Emmemad/ATS-20_Schematic/ATS-20+/ATS-20_Plus_Trace/Images/encoder_ribbon_cable_socket.jpg

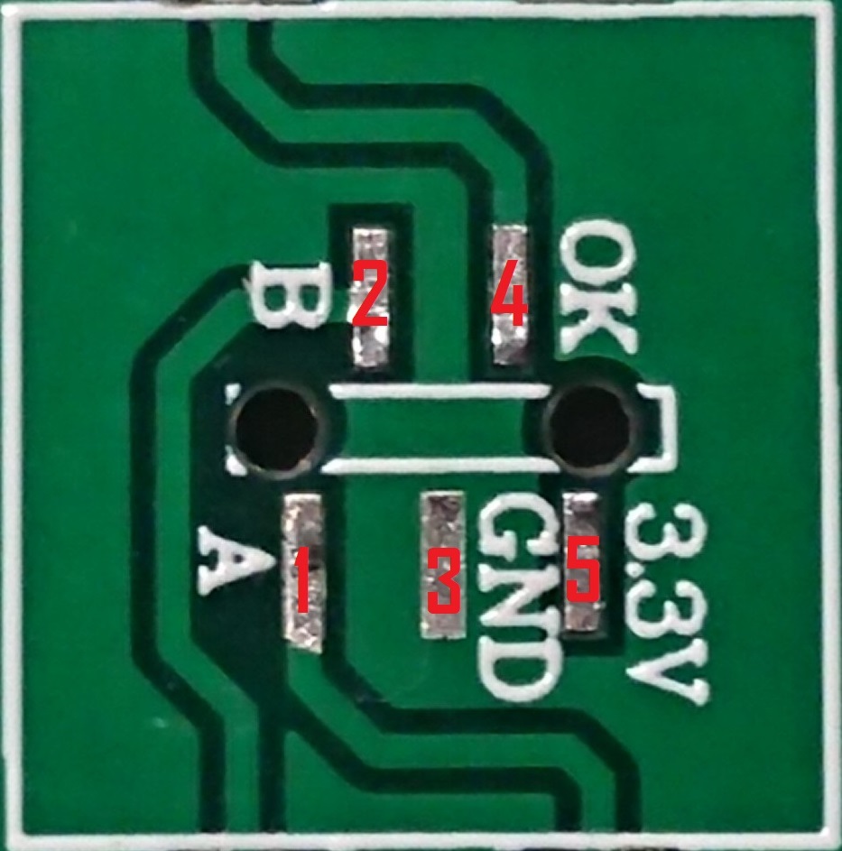
ATS-20+/ATS-20_Plus_Trace/Images/encoder_ribbon_cable_socket.jpg
