Emmemad/ATS-20_Schematic/ATS-20+/ATS-20_Plus_Trace/Images/ribbon_cable_socket.png

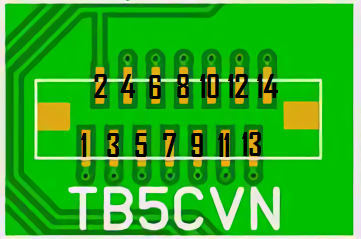
ATS-20+/ATS-20_Plus_Trace/Images/ribbon_cable_socket.png
