Emmemad/ATS-20_Schematic/ATS-20+/Pictures/ATS-20+_charging_port.png

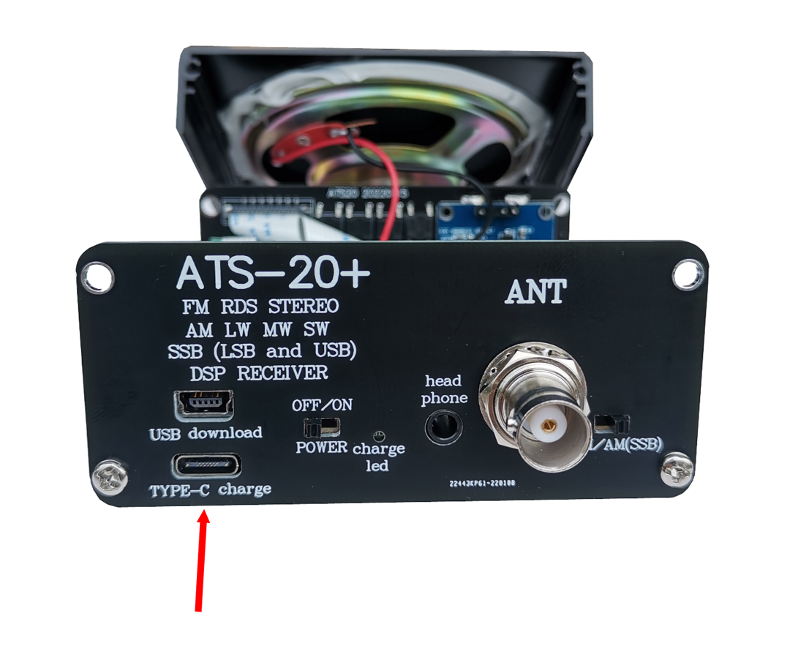
ATS-20+/Pictures/ATS-20+_charging_port.png
