Emmemad/ATS-20_Schematic/ATS-20+/Pictures/ATS-20+_encoder.jpg

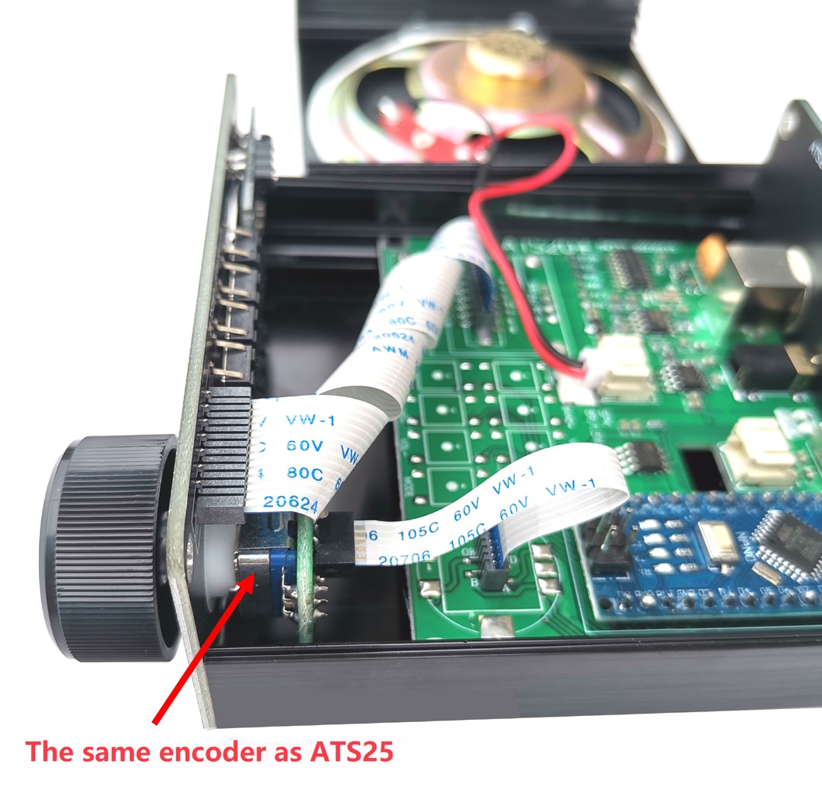
ATS-20+/Pictures/ATS-20+_encoder.jpg
