Emmemad/ATS-20_Schematic/ATS-20+/Pictures/ATS-20+_filter_amplifier.jpg

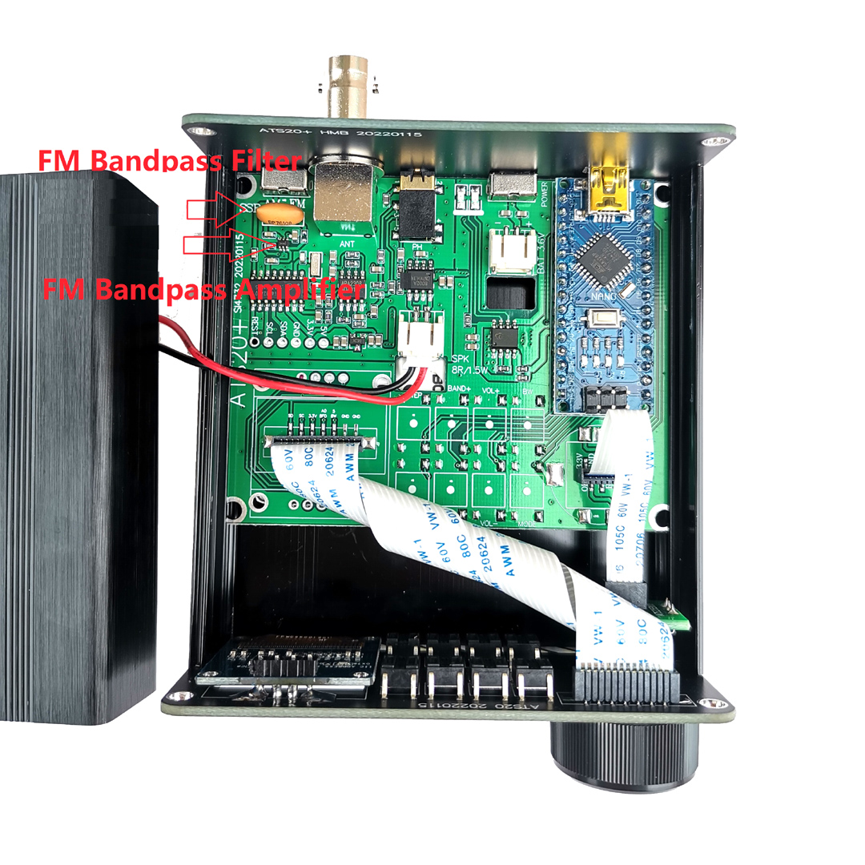
ATS-20+/Pictures/ATS-20+_filter_amplifier.jpg
