Emmemad/ATS-20_Schematic/ATS-20+/Pictures/Board_photos/ATS-20_Plus_7.JPG

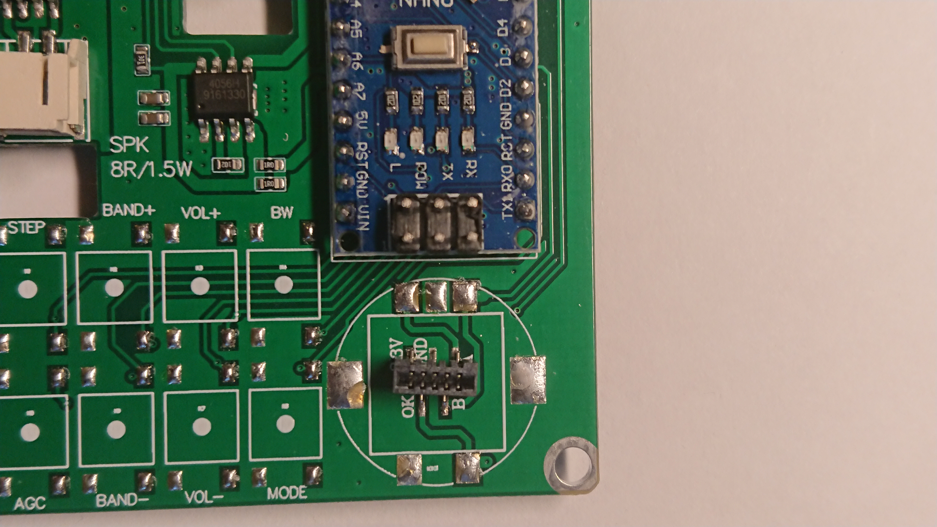
ATS-20+/Pictures/Board_photos/ATS-20_Plus_7.JPG
