Emmemad/ATS-20_Schematic/ATS-20/Pictures/ATS-20_back_antenna.jpg

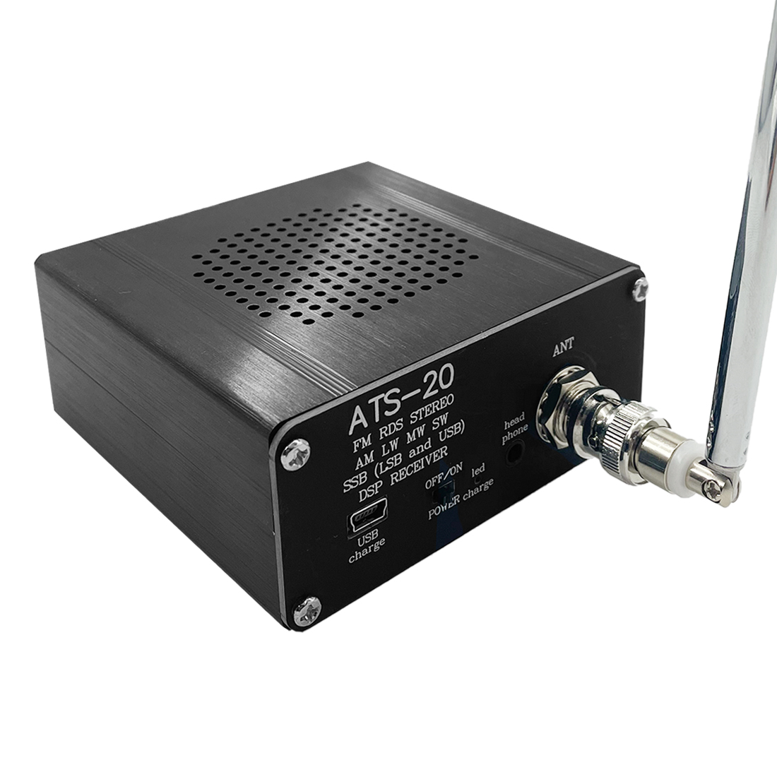
ATS-20/Pictures/ATS-20_back_antenna.jpg
