Emmemad/ATS-20_Schematic/ATS-20/Pictures/ATS-20_cover_removed.JPG

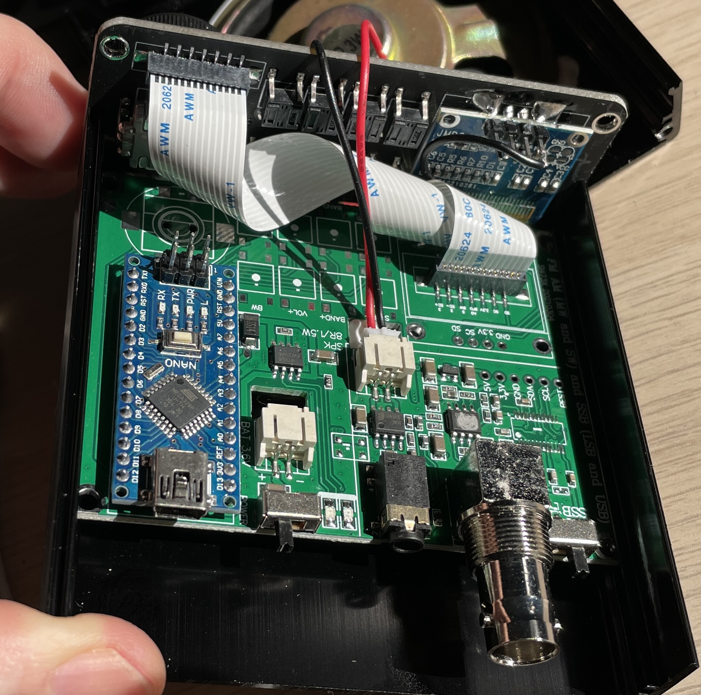
ATS-20/Pictures/ATS-20_cover_removed.JPG
