Emmemad/ATS-20_Schematic/ATS-20/Pictures/PCB/Original/1110541948202.jpg

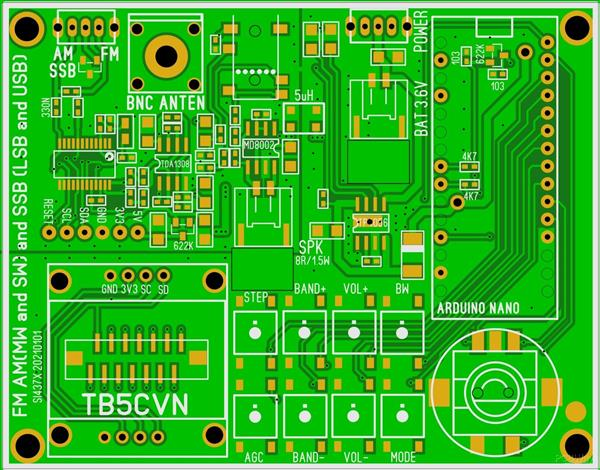
ATS-20/Pictures/PCB/Original/1110541948202.jpg
