Emmemad/ATS-20_Schematic/ATS-20/Pictures/PCB/Original/1111073910710.jpg

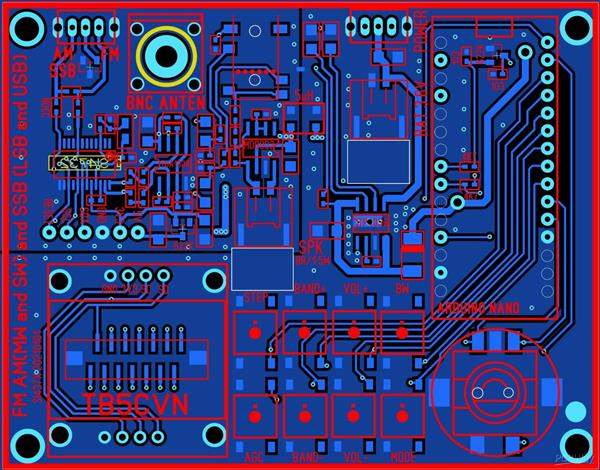
ATS-20/Pictures/PCB/Original/1111073910710.jpg
