Emmemad/ATS-20_Schematic/ATS-20/Pictures/PCB/Original/1111167664805.jpg

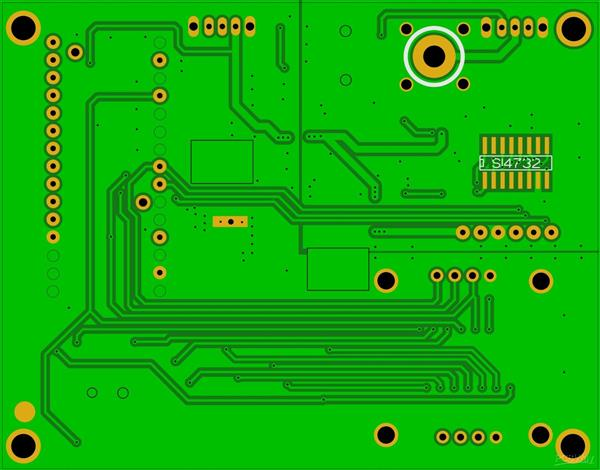
ATS-20/Pictures/PCB/Original/1111167664805.jpg
