Emmemad/ATS-20_Schematic/ATS-20/Pictures/PCB/Traceback enhanced/TB5CVN_back_enhanced_mirrored.png

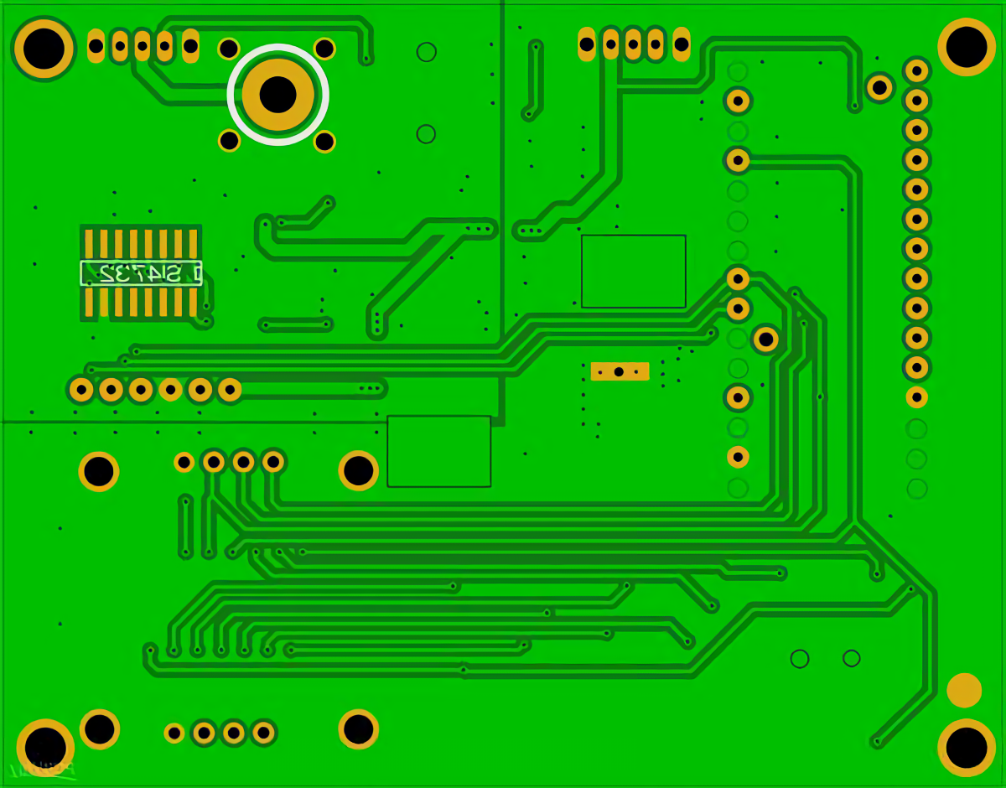
ATS-20/Pictures/PCB/Traceback enhanced/TB5CVN_back_enhanced_mirrored.png
