Emmemad/ATS-20_Schematic/ATS-20/Pictures/Robert Richmond's photos/Si4732-Internal-Photos-Robert-Richmond-2.jpeg

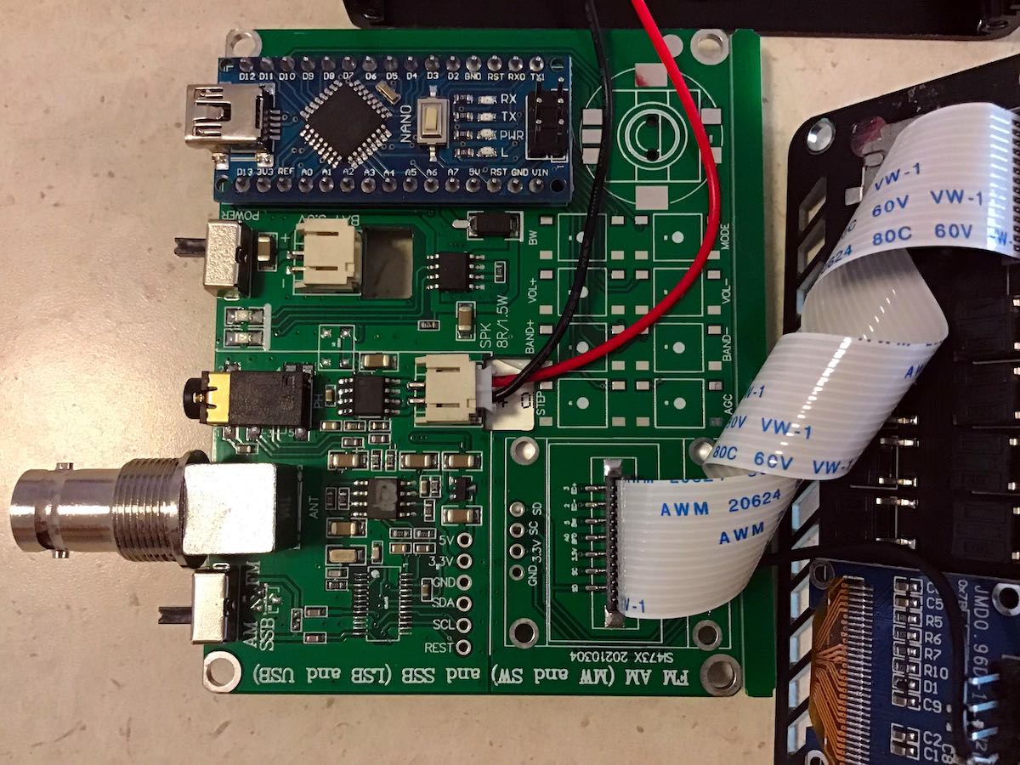
ATS-20/Pictures/Robert Richmond's photos/Si4732-Internal-Photos-Robert-Richmond-2.jpeg
