Emmemad/ATS-20_Schematic/ATS-20+/ATS-20_Plus_Trace/ATS-20_Plus_Trace.kicad_sch

## KiCad design ATS-20+/ATS-20_Plus_Trace/ATS-20_Plus_Trace.kicad_sch (2022-08-20)

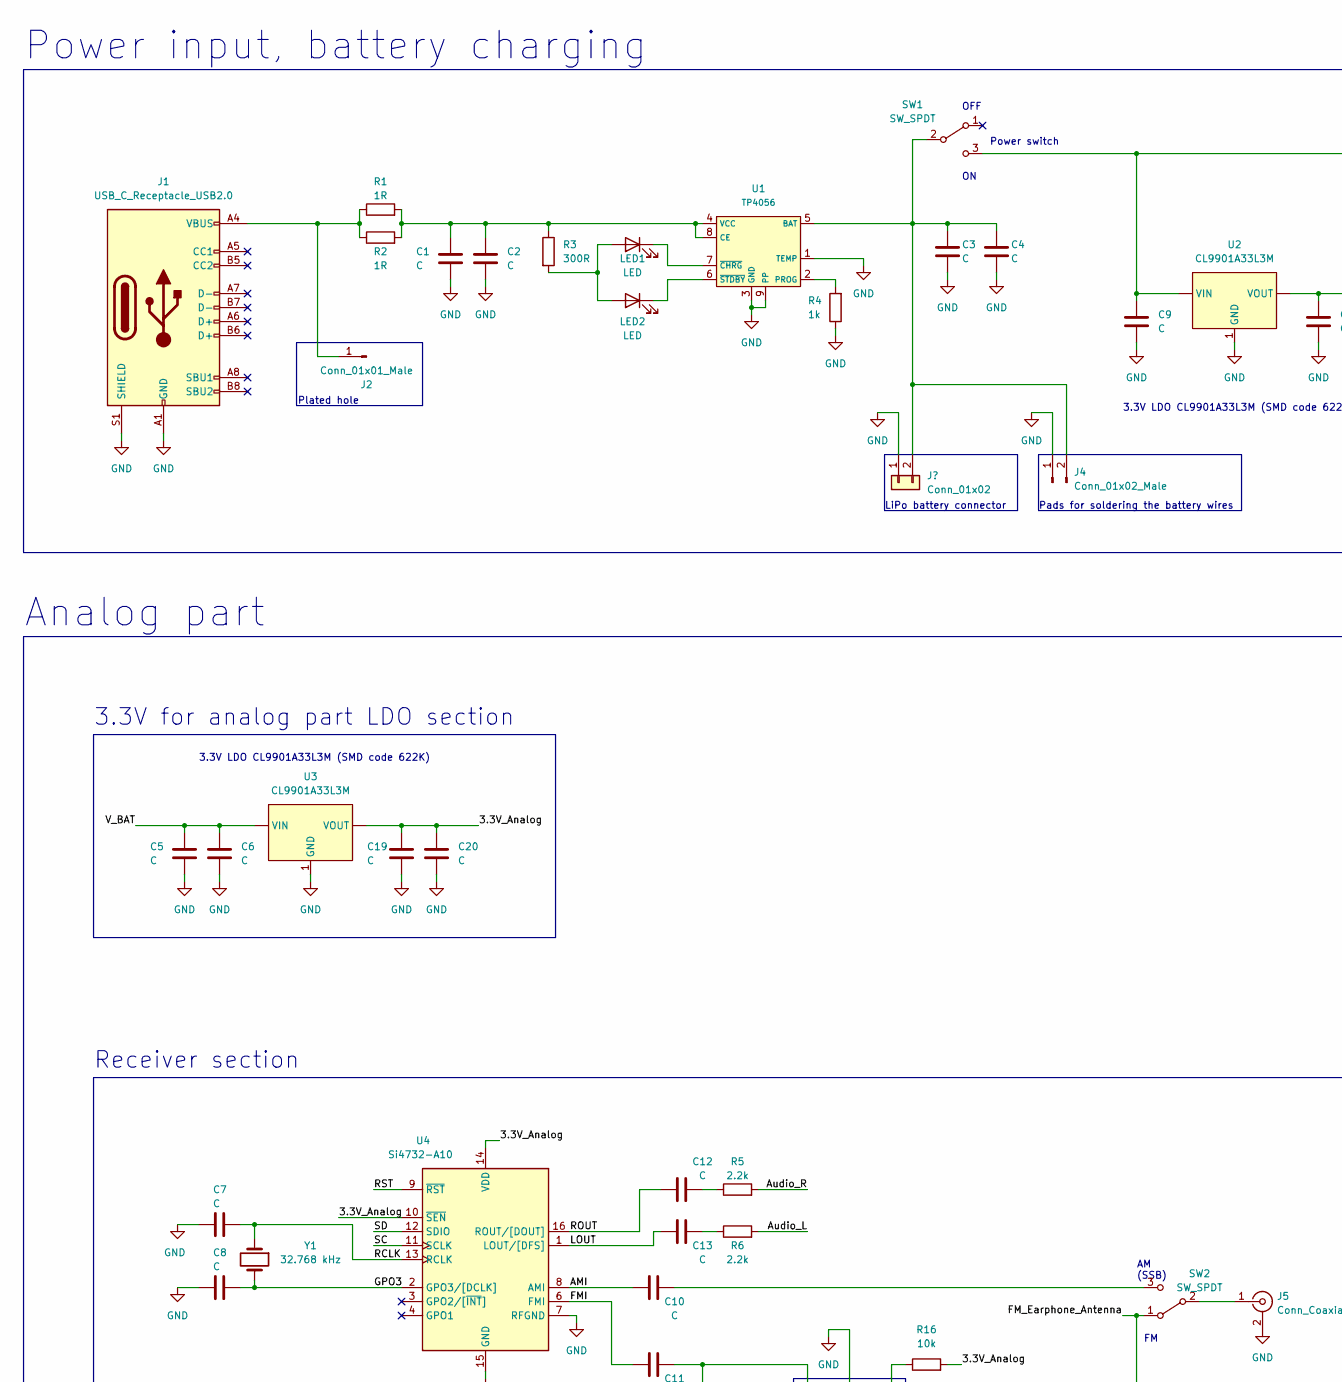
[picture p44: schematic ATS-20_Plus_Trace.kicad_sch, part in row 1, column 1]

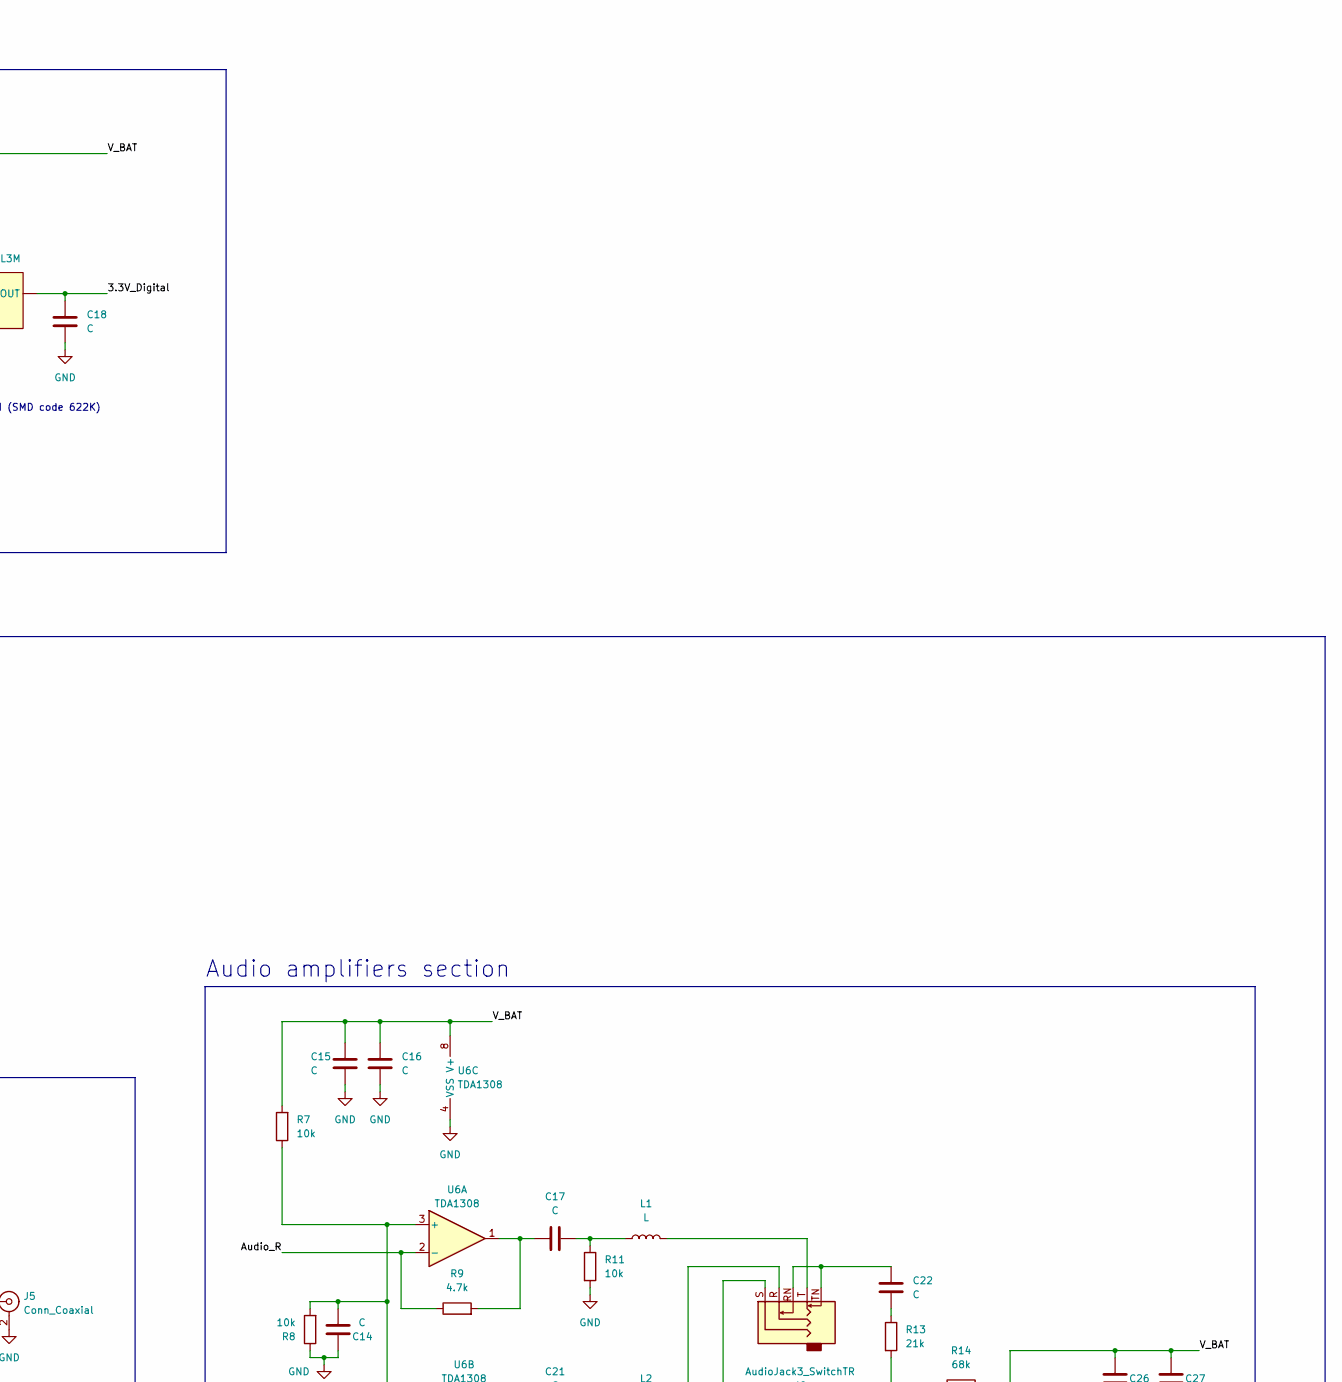
[picture p45: schematic ATS-20_Plus_Trace.kicad_sch, part in row 1, column 2]

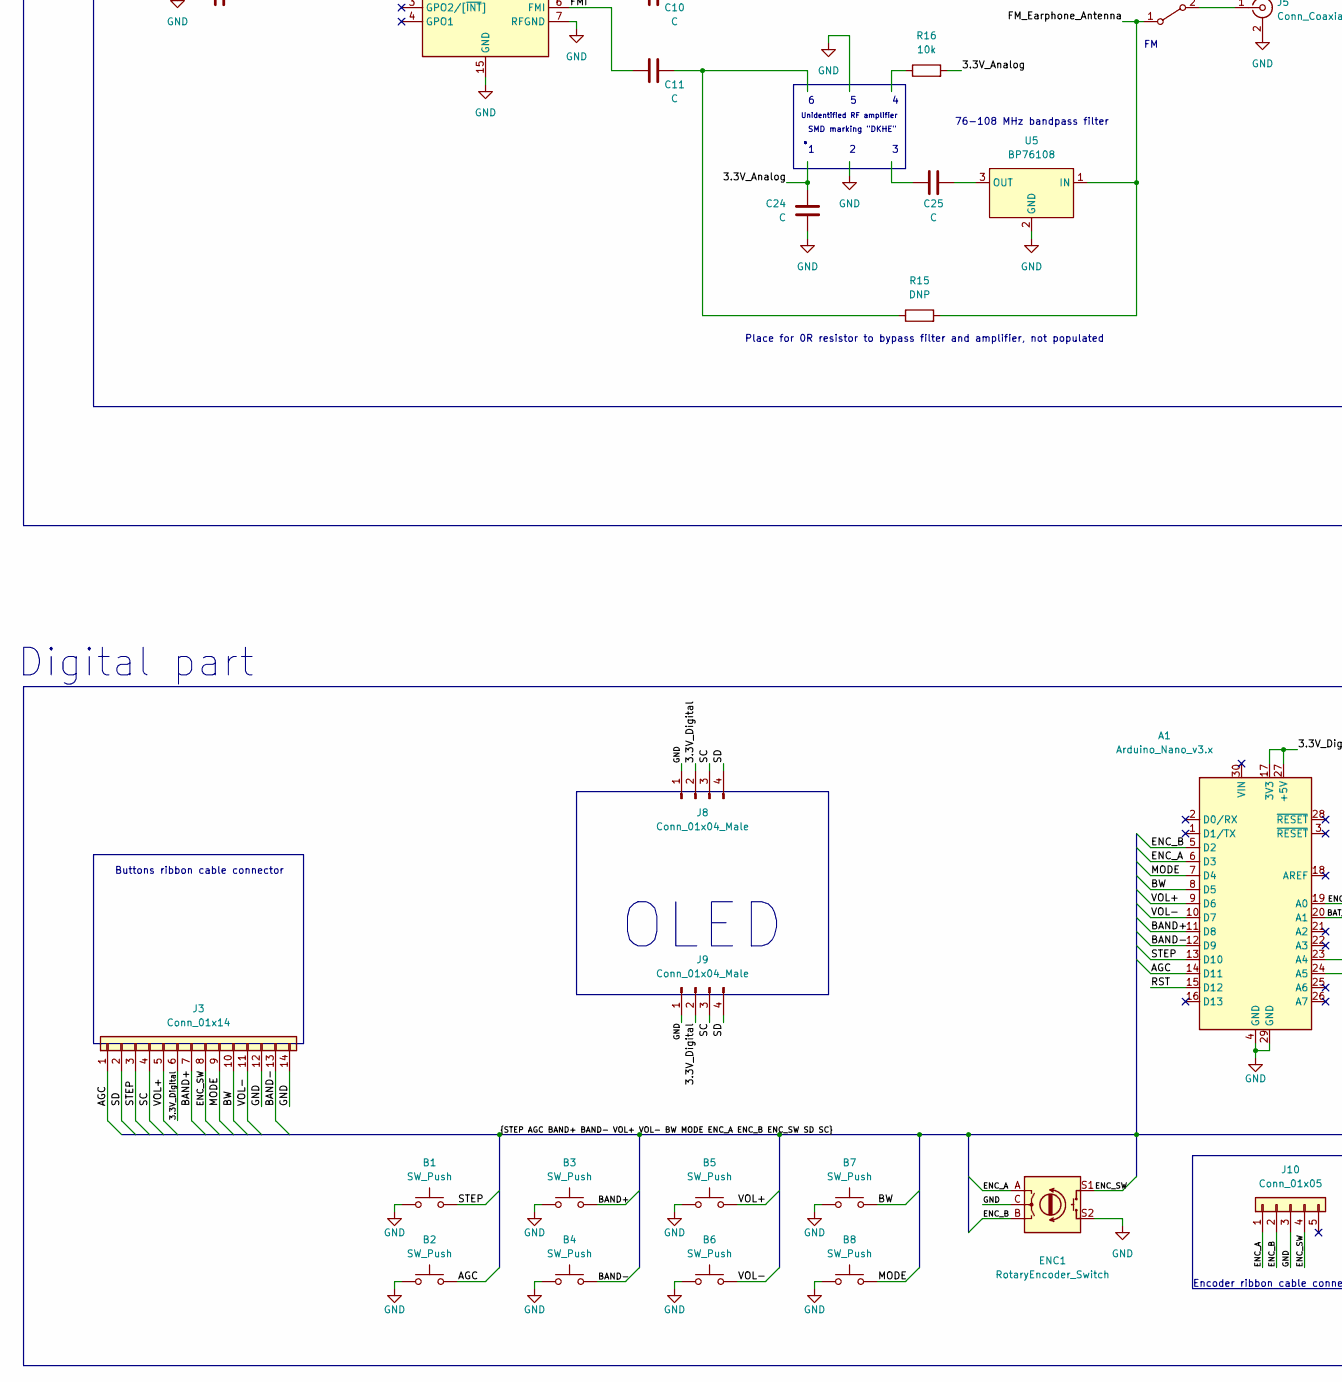
[picture p46: schematic ATS-20_Plus_Trace.kicad_sch, part in row 2, column 1]

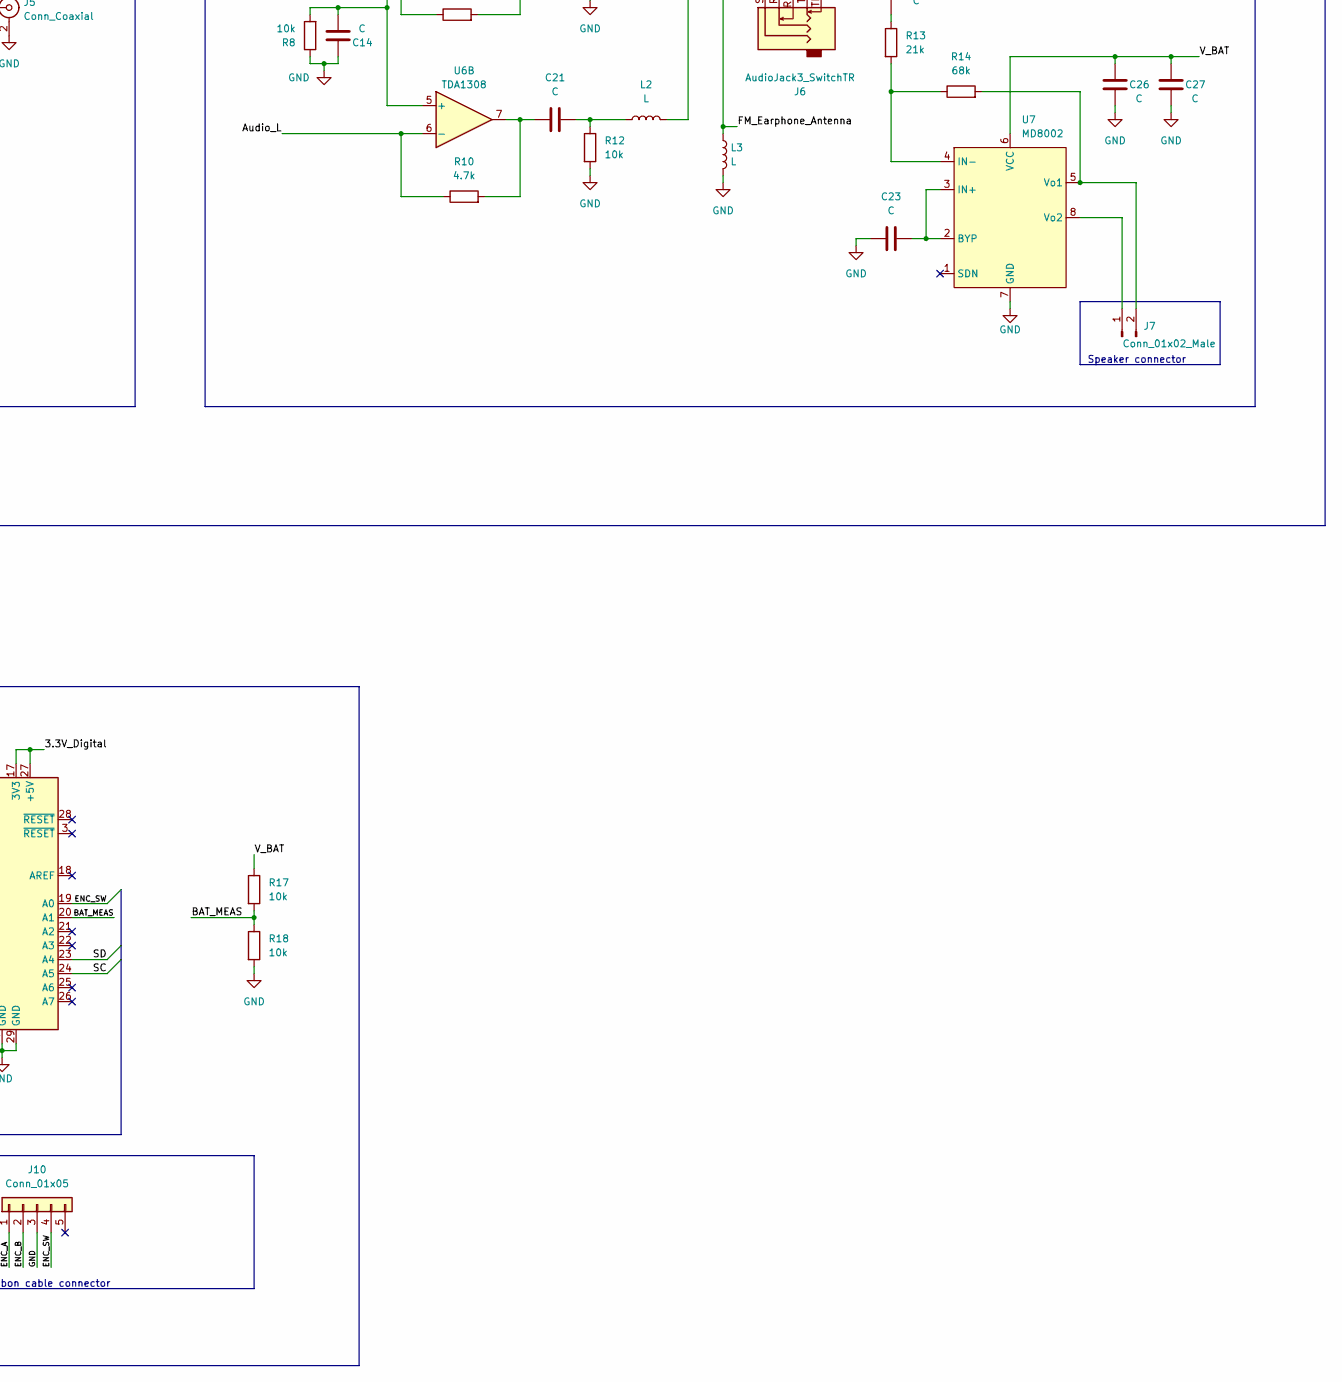
[picture p47: schematic ATS-20_Plus_Trace.kicad_sch, part in row 2, column 2]

Parts:
A1: Arduino_Nano_v3.x; Arduino_Nano
B1, B2, B3, B4, B5, B6, B7, B8: SW_Push
C1, C2, C3, C4, C5, C6, C7, C8, C9, C10, C11, C12, C13, C14, C15, C16, C17, C18, C19, C20, C21, C22, C23, C24, C25, C26, C27: C
ENC1: RotaryEncoder_Switch
J1: USB_C_Receptacle_USB2.0
J2: Conn_01x01_Male
J3: Conn_01x14; Molex_PicoBlade_53398-1471_1x14-1MP_P1.25mm_Vertical
J4, J7: Conn_01x02_Male
J5: Conn_Coaxial
J6: AudioJack3_SwitchTR; Jack_3.5mm_PJ311_Horizontal
J8, J9: Conn_01x04_Male
J10: Conn_01x05
L1, L2, L3: L
LED1, LED2: LED
R1, R2: 1R
R3: 300R
R4: 1k
R5, R6: 2.2k
R7, R8, R11, R12, R16, R17, R18: 10k
R9, R10: 4.7k
R13: 21k
R14: 68k
R15: DNP
SW1, SW2: SW_SPDT
U1: TP4056; SOIC-8-1EP_3.9x4.9mm_P1.27mm_EP2.29x3mm
U2, U3: CL9901A33L3M
U4: Si4732-A10; SOIC-16_4.55x10.3mm_P1.27mm
U5: BP76108
U6: TDA1308
U7: MD8002
Y1: 32.768 kHz

Connections:
3.3V_Analog: C19.1, C20.1, C24.1, R16.2, U3. (VIN), U4.10 (~SEN), U4.14 (VDD)
3.3V_Digital: A1.17 (3V3), A1.27 (+5V), C18.1, J3.6, J8.2, J9.2, U2. (VIN)
AGC: A1.14 (D11), B2.2, J3.1
AMI: C10.1, U4.8 (AMI)
Audio_L: R6.2, R10.1, U6.6 (-)
Audio_R: R5.2, R9.1, U6.2 (-)
BAND+: A1.11 (D8), B3.2, J3.7
BAND-: A1.12 (D9), B4.2, J3.13
BAT_MEAS: A1.20 (A1), R17.2, R18.1
BW: A1.8 (D5), B7.2, J3.10
ENC_A: A1.6 (D3), ENC1.A, J10.1
ENC_B: A1.5 (D2), ENC1.B, J10.2
ENC_SW: A1.19 (A0), ENC1.S1, J3.8, J10.4
FMI: C11.1, U4.6 (FMI)
FM_Earphone_Antenna: J6.S, L3.1, R15.2, SW2.1 (A), U5.1 (IN)
GND: A1.4 (GND), A1.29 (GND), B1.1, B2.1, B3.1, B4.1, B5.1, B6.1, B7.1, B8.1, C1.1, C2.1, C3.1, C4.1, C5.2, C6.2, C7.2, C8.2, C9.2, C14.1, C15.2, C16.2, C18.2, C19.2, C20.2, C23.2, C24.2, C26.2, C27.2, ENC1.C, ENC1.S2, J1.A1 (GND), J1.A12 (GND), J1.B1 (GND), J1.B12 (GND), J1.S1 (SHIELD), J3.12, J3.14, J4.1, J5.2 (Ext), J8.1, J9.1, J10.3, L3.2, R4.1, R8.1, R11.2, R12.2, R18.2, U1.1 (TEMP), U1.3 (GND), U1.9 (PP), U2.1 (GND), U3.1 (GND), U4.7 (RFGND), U4.15 (GND), U5.2 (GND), U6.4 (VSS), U7.7 (GND)
GPO3: C8.1, U4.2 (GPO3/[DCLK]), Y1.2
LOUT: C13.1, U4.1 (LOUT/[DFS])
MODE: A1.7 (D4), B8.2, J3.9
unnamed: C1.2, C2.2, R1.2, R2.2, R3.1, U1.4 (VCC), U1.8 (CE)
unnamed: C3.2, C4.2, J4.2, SW1.2 (B), U1.5 (BAT)
unnamed: C10.2, SW2.3 (C)
unnamed: C11.2, R15.1
unnamed: C12.2, R5.1
unnamed: C13.2, R6.1
unnamed: C14.2, R7.1, R8.2, U6.3 (+), U6.5 (+)
unnamed: C17.1, R9.2, U6.1
unnamed: C17.2, L1.1, R11.1
unnamed: C21.1, R10.2, U6.7
unnamed: C21.2, L2.1, R12.1
unnamed: C22.1, J6.RN, J6.TN
unnamed: C22.2, R13.1
unnamed: C23.1, U7.2 (BYP), U7.3 (IN+)
unnamed: C25.2, U5.3 (OUT)
unnamed: J1.A4 (VBUS), J1.A9 (VBUS), J1.B4 (VBUS), J1.B9 (VBUS), J2.1, R1.1, R2.1
unnamed: J5.1 (In), SW2.2 (B)
unnamed: J6.R, L2.2
unnamed: J6.T, L1.2
unnamed: J7.1, U7.8 (Vo2)
unnamed: J7.2, R14.2, U7.5 (Vo1)
unnamed: LED1.1 (K), U1.7 (~CHRG)
unnamed: LED1.2 (A), LED2.2 (A), R3.2
unnamed: LED2.1 (K), U1.6 (~STDBY)
unnamed: R4.2, U1.2 (PROG)
unnamed: R13.2, R14.1, U7.4 (IN-)
RCLK: C7.1, U4.13 (RCLK), Y1.1
ROUT: C12.1, U4.16 (ROUT/[DOUT])
RST: A1.15 (D12), U4.9 (~RST)
SC: A1.24 (A5), J3.4, J8.3, J9.3, U4.11 (SCLK)
SD: A1.23 (A4), J3.2, J8.4, J9.4, U4.12 (SDIO)
STEP: A1.13 (D10), B1.2, J3.3
VOL+: A1.9 (D6), B5.2, J3.5
VOL-: A1.10 (D7), B6.2, J3.11
V_BAT: C5.1, C6.1, C9.1, C15.1, C16.1, C26.1, C27.1, R7.2, R17.1, SW1.3 (C), U2. (VIN), U3. (VIN), U6.8 (V+), U7.6 (VCC)

Notes on the sheet:
Place for 0R resistor to bypass filter and amplifier, not populated
Unidentified RF amplifier
Power switch
Encoder ribbon cable connector
Analog part
AM (SSB)
Pads for soldering the battery wires
Digital part
3.3V LDO CL9901A33L3M (SMD code 622K)
OLED
76-108 MHz bandpass filter
Plated hole
Audio amplifiers section
Buttons ribbon cable connector
Speaker connector
SMD marking "DKHE"
Power input, battery charging
3.3V for analog part LDO section
Receiver section
LiPo battery connector
OFF
