Emmemad/ATS-20_Schematic/ATS-20/ATS-20_TB5CVN_Trace/ATS-20_TB5CVN_Trace.kicad_sch

## KiCad design ATS-20/ATS-20_TB5CVN_Trace/ATS-20_TB5CVN_Trace.kicad_sch (2022-08-20)

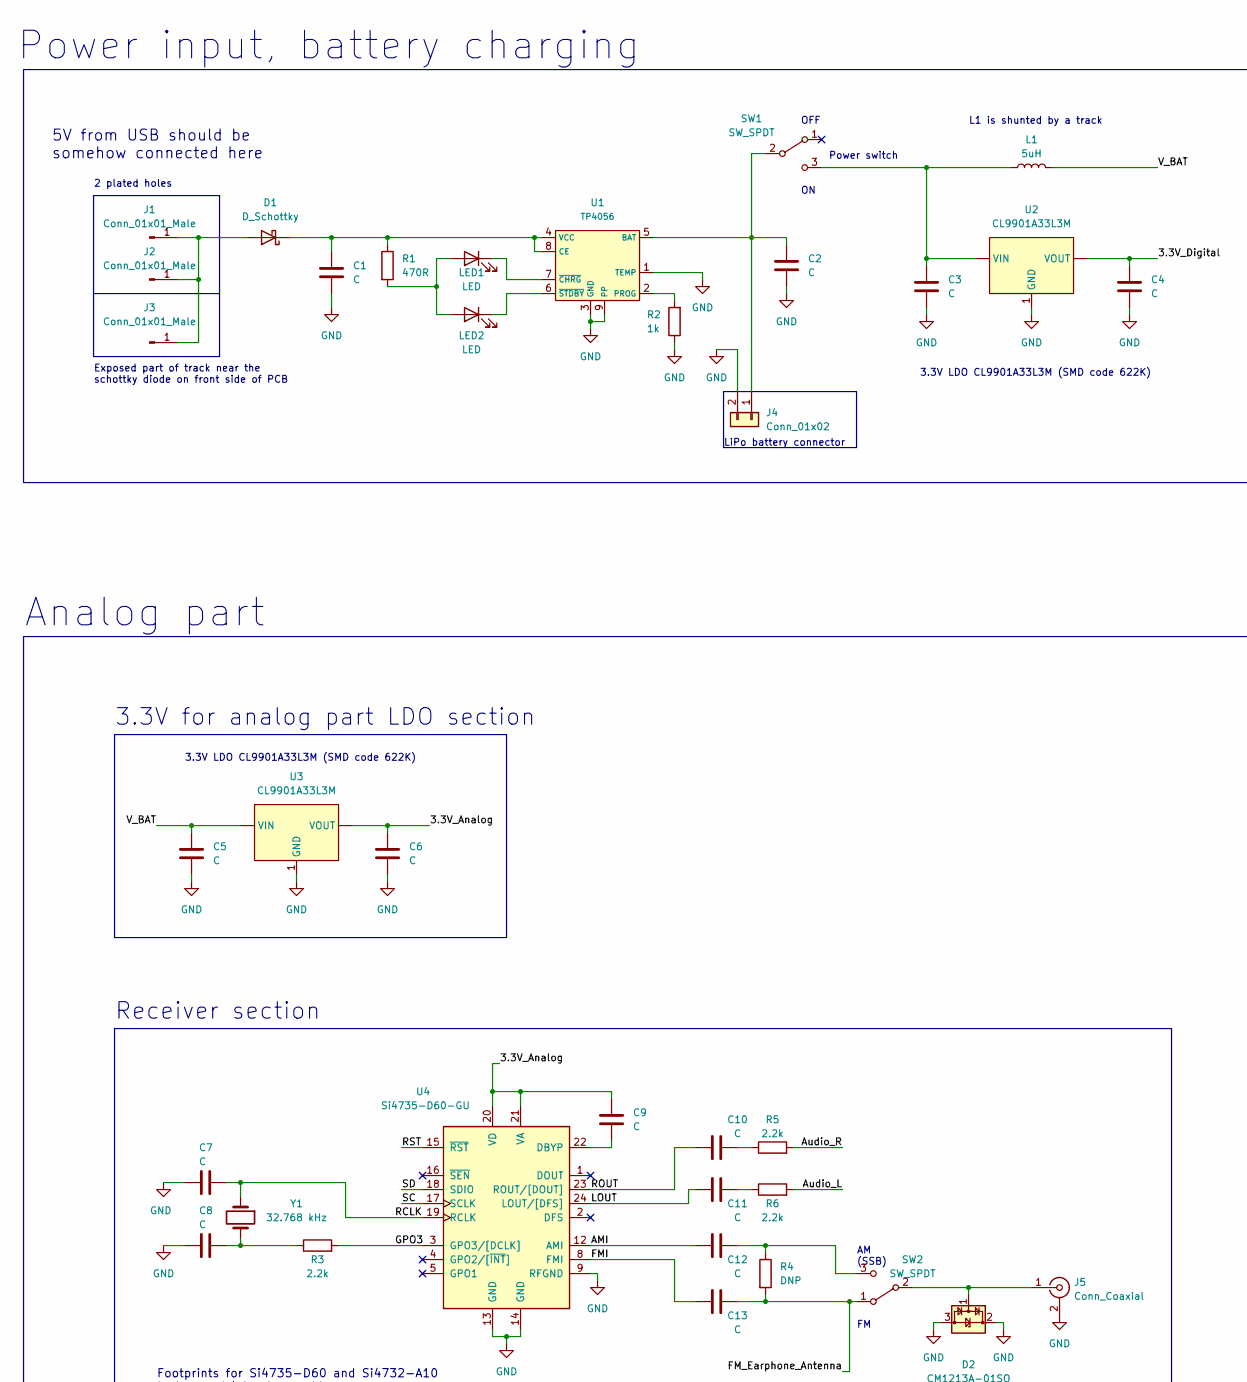
[picture p48: schematic ATS-20_TB5CVN_Trace.kicad_sch, part in row 1, column 1]

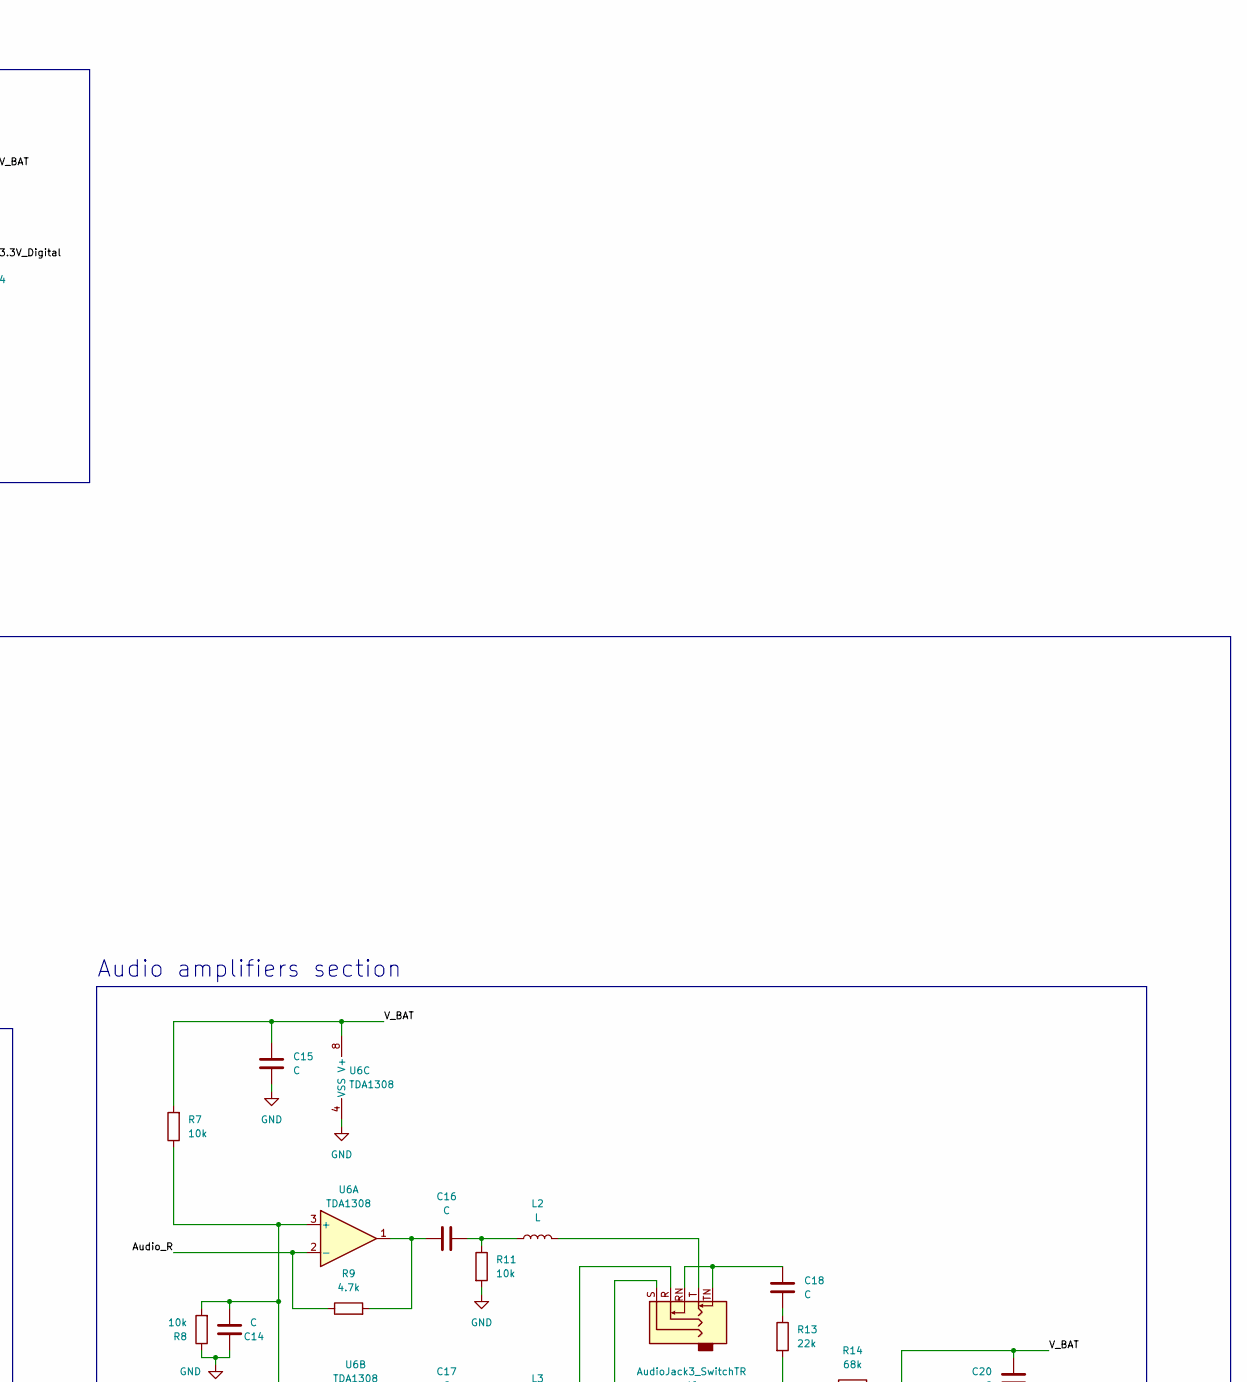
[picture p49: schematic ATS-20_TB5CVN_Trace.kicad_sch, part in row 1, column 2]

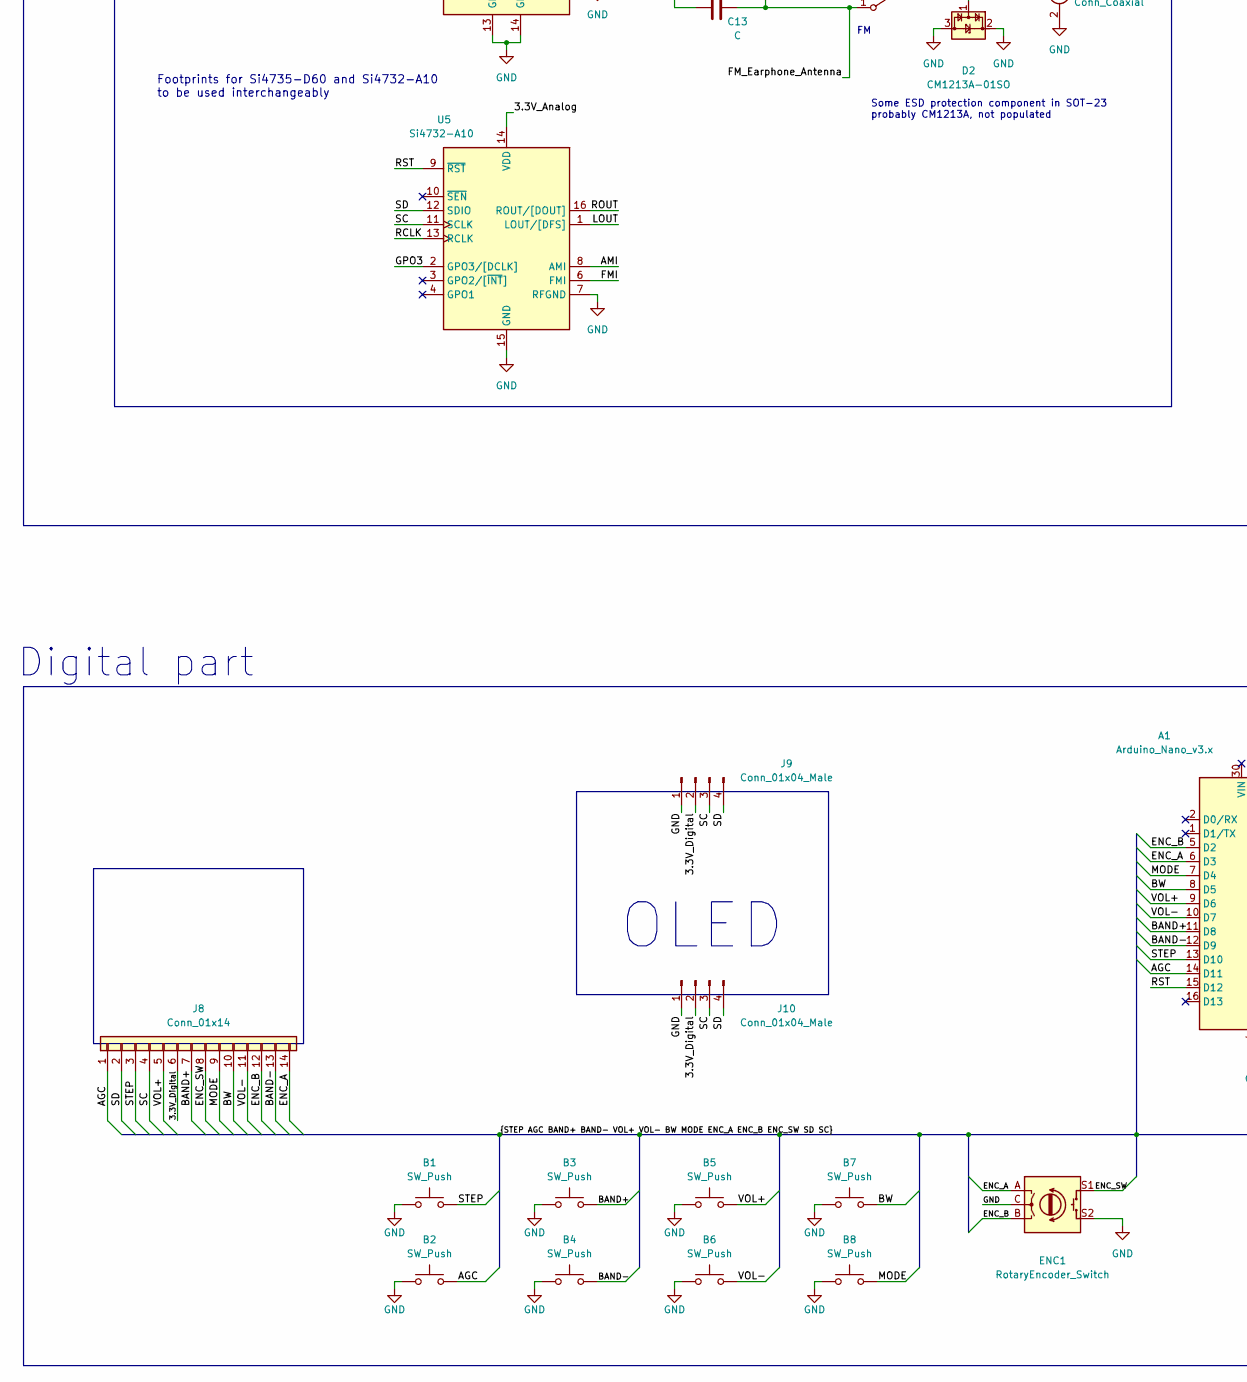
[picture p50: schematic ATS-20_TB5CVN_Trace.kicad_sch, part in row 2, column 1]

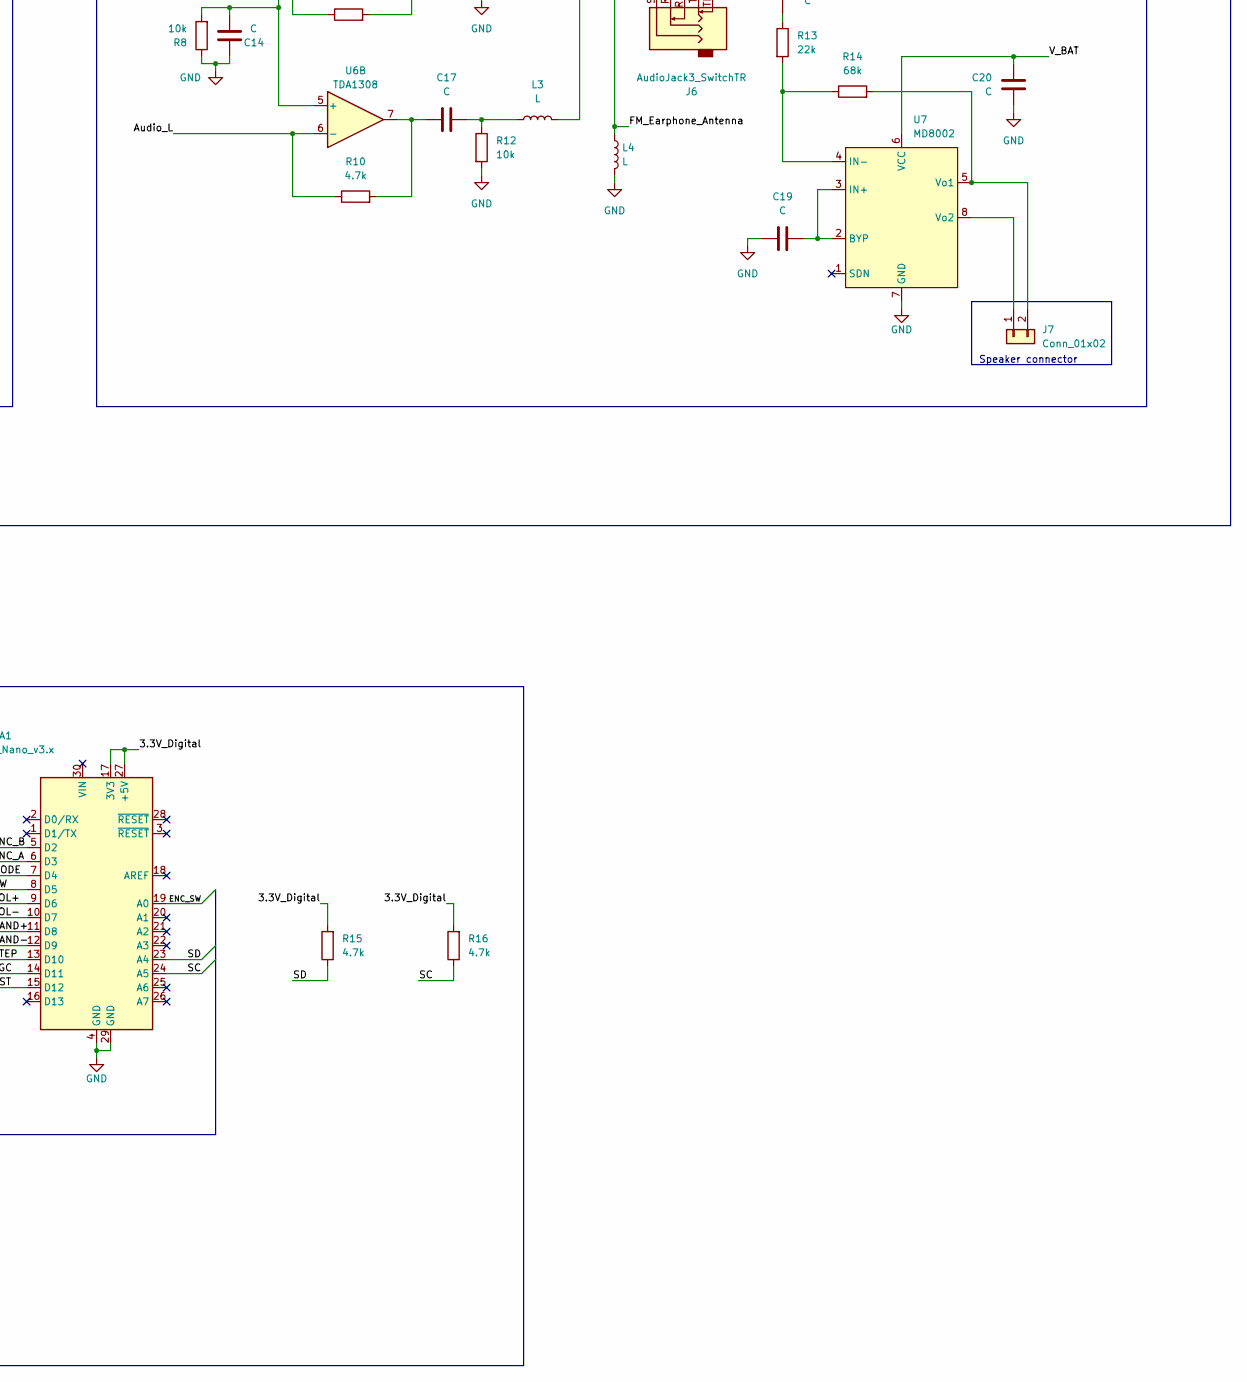
[picture p51: schematic ATS-20_TB5CVN_Trace.kicad_sch, part in row 2, column 2]

Parts:
A1: Arduino_Nano_v3.x; Arduino_Nano
B1, B2, B3, B4, B5, B6, B7, B8: SW_Push
C1, C2, C3, C4, C5, C6, C7, C8, C9, C10, C11, C12, C13, C14, C15, C16, C17, C18, C19, C20: C
D1: D_Schottky
D2: CM1213A-01SO; SOT-23
ENC1: RotaryEncoder_Switch
J1, J2, J3: Conn_01x01_Male
J4, J7: Conn_01x02
J5: Conn_Coaxial
J6: AudioJack3_SwitchTR; Jack_3.5mm_PJ311_Horizontal
J8: Conn_01x14; Molex_PicoBlade_53398-1471_1x14-1MP_P1.25mm_Vertical
J9, J10: Conn_01x04_Male
L1: 5uH
L2, L3, L4: L
LED1, LED2: LED
R1: 470R
R2: 1k
R3, R5, R6: 2.2k
R4: DNP
R7, R8, R11, R12: 10k
R9, R10, R15, R16: 4.7k
R13: 22k
R14: 68k
SW1, SW2: SW_SPDT
U1: TP4056; SOIC-8-1EP_3.9x4.9mm_P1.27mm_EP2.29x3mm
U2, U3: CL9901A33L3M
U4: Si4735-D60-GU; SSOP-24_3.9x8.7mm_P0.635mm
U5: Si4732-A10; SOIC-16_4.55x10.3mm_P1.27mm
U6: TDA1308
U7: MD8002
Y1: 32.768 kHz

Connections:
3.3V_Analog: C6.1, C9.1, U3. (VIN), U4.20 (VD), U4.21 (VA), U5.14 (VDD)
3.3V_Digital: A1.17 (3V3), A1.27 (+5V), C4.1, J8.6, J9.2, J10.2, R15.2, R16.2, U2. (VIN)
AGC: A1.14 (D11), B2.2, J8.1
AMI: C12.1, U4.12 (AMI), U5.8 (AMI)
Audio_L: R6.2, R10.1, U6.6 (-)
Audio_R: R5.2, R9.1, U6.2 (-)
BAND+: A1.11 (D8), B3.2, J8.7
BAND-: A1.12 (D9), B4.2, J8.13
BW: A1.8 (D5), B7.2, J8.10
ENC_A: A1.6 (D3), ENC1.A, J8.14
ENC_B: A1.5 (D2), ENC1.B, J8.12
ENC_SW: A1.19 (A0), ENC1.S1, J8.8
FMI: C13.1, U4.8 (FMI), U5.6 (FMI)
FM_Earphone_Antenna: C13.2, J6.S, L4.1, R4.2, SW2.1 (A)
GND: A1.4 (GND), A1.29 (GND), B1.1, B2.1, B3.1, B4.1, B5.1, B6.1, B7.1, B8.1, C1.1, C2.1, C3.2, C4.2, C5.2, C6.2, C7.2, C8.2, C14.1, C15.2, C19.2, C20.2, D2.2 (VP), D2.3 (VN), ENC1.C, ENC1.S2, J4.2, J5.2 (Ext), J9.1, J10.1, L4.2, R2.1, R8.1, R11.2, R12.2, U1.1 (TEMP), U1.3 (GND), U1.9 (PP), U2.1 (GND), U3.1 (GND), U4.9 (RFGND), U4.13 (GND), U4.14 (GND), U5.7 (RFGND), U5.15 (GND), U6.4 (VSS), U7.7 (GND)
GPO3: R3.2, U4.3 (GPO3/[DCLK]), U5.2 (GPO3/[DCLK])
LOUT: C11.1, U4.24 (LOUT/[DFS]), U5.1 (LOUT/[DFS])
MODE: A1.7 (D4), B8.2, J8.9
unnamed: C1.2, D1.1 (K), R1.1, U1.4 (VCC), U1.8 (CE)
unnamed: C2.2, J4.1, SW1.2 (B), U1.5 (BAT)
unnamed: C3.1, L1.1, SW1.3 (C), U2. (VIN)
unnamed: C8.1, R3.1, Y1.2
unnamed: C9.2, U4.22 (DBYP)
unnamed: C10.2, R5.1
unnamed: C11.2, R6.1
unnamed: C12.2, R4.1, SW2.3 (C)
unnamed: C14.2, R7.1, R8.2, U6.3 (+), U6.5 (+)
unnamed: C16.1, R9.2, U6.1
unnamed: C16.2, L2.1, R11.1
unnamed: C17.1, R10.2, U6.7
unnamed: C17.2, L3.1, R12.1
unnamed: C18.1, J6.RN, J6.TN
unnamed: C18.2, R13.1
unnamed: C19.1, U7.2 (BYP), U7.3 (IN+)
unnamed: D1.2 (A), J1.1, J2.1, J3.1
unnamed: D2.1 (CH1), J5.1 (In), SW2.2 (B)
unnamed: J6.R, L3.2
unnamed: J6.T, L2.2
unnamed: J7.1, U7.8 (Vo2)
unnamed: J7.2, R14.2, U7.5 (Vo1)
unnamed: LED1.1 (K), U1.7 (~CHRG)
unnamed: LED1.2 (A), LED2.2 (A), R1.2
unnamed: LED2.1 (K), U1.6 (~STDBY)
unnamed: R2.2, U1.2 (PROG)
unnamed: R13.2, R14.1, U7.4 (IN-)
RCLK: C7.1, U4.19 (RCLK), U5.13 (RCLK), Y1.1
ROUT: C10.1, U4.23 (ROUT/[DOUT]), U5.16 (ROUT/[DOUT])
RST: A1.15 (D12), U4.15 (~RST), U5.9 (~RST)
SC: A1.24 (A5), J8.4, J9.3, J10.3, R16.1, U4.17 (SCLK), U5.11 (SCLK)
SD: A1.23 (A4), J8.2, J9.4, J10.4, R15.1, U4.18 (SDIO), U5.12 (SDIO)
STEP: A1.13 (D10), B1.2, J8.3
VOL+: A1.9 (D6), B5.2, J8.5
VOL-: A1.10 (D7), B6.2, J8.11
V_BAT: C5.1, C15.1, C20.1, L1.2, R7.2, U3. (VIN), U6.8 (V+), U7.6 (VCC)

Notes on the sheet:
Power switch
5V from USB should be somehow connected here
L1 is shunted by a track
Analog part
AM (SSB)
Digital part
3.3V LDO CL9901A33L3M (SMD code 622K)
OLED
2 plated holes
Audio amplifiers section
Speaker connector
Some ESD protection component in SOT-23 probably CM1213A, not populated
Exposed part of track near the schottky diode on front side of PCB
Footprints for Si4735-D60 and Si4732-A10 to be used interchangeably
Power input, battery charging
3.3V for analog part LDO section
Receiver section
LiPo battery connector
OFF
